Licheng-Zheng/Macropad/Firmware and Building/tusb_config.h

#ifndef _TUSB_CONFIG_H_
#define _TUSB_CONFIG_H_

#define CFG_TUSB_RHPORT0_MODE   OPT_MODE_DEVICE
#define CFG_TUD_ENDPOINT0_SIZE  64

// Enable 1 HID Interface
#define CFG_TUD_HID             1
#define CFG_TUD_CDC             0
#define CFG_TUD_MSC             0
#define CFG_TUD_MIDI            0
#define CFG_TUD_VENDOR          0

// HID buffer size
#define CFG_TUD_HID_EP_BUFSIZE  16

#endif
